aotta/SD-1000/Source/CVBasic/logo.bas

	' TMSColor 2.2.1 Mar/29/2024
	' Command: C:\Users\Andrea\Documents\Retrocomputer\SEGA\SG-1000\CVBasic\tmscolor.exe -z -b -p1 sega_logo6.bmp logo.bas 
	' Created: Sun Apr 14 18:44:49 2024

image_bitmap:
	DATA BYTE $7a,$00,$ba,$eb,$02,$00,$03,$0f
	DATA BYTE $1f,$3f,$7f,$06,$0a,$7f,$ff,$ff
	DATA BYTE $80,$02,$07,$ba,$03,$00,$07,$02
	DATA BYTE $f8,$f8,$fb,$3f,$3f,$3e,$07,$46
	DATA BYTE $1f,$0c,$e0,$80,$e6,$17,$28,$04
	DATA BYTE $07,$00,$07,$07,$1f,$0f,$7f,$fc
	DATA BYTE $e0,$c0,$45,$17,$01,$00,$21,$07
	DATA BYTE $c0,$00,$c1,$c3,$c3,$90,$37,$50
	DATA BYTE $f0,$c0,$80,$80,$07,$e0,$f8,$fc
	DATA BYTE $fe,$0f,$07,$f2,$6b,$0f,$d5,$7e
	DATA BYTE $00,$c0,$ab,$61,$03,$00,$f0,$e0
	DATA BYTE $01,$ac,$83,$86,$0c,$00,$ff,$7f
	DATA BYTE $c0,$fd,$04,$1f,$ec,$1e,$0c,$00
	DATA BYTE $3e,$fc,$38,$00,$86,$83,$12,$03
	DATA BYTE $30,$60,$40,$40,$41,$41,$e6,$17
	DATA BYTE $07,$00,$fc,$06,$06,$fe,$03,$fe
	DATA BYTE $80,$03,$07,$0c,$18,$36,$00,$15
	DATA BYTE $1a,$7f,$7f,$01,$04,$fd,$04,$c7
	DATA BYTE $90,$00,$cf,$00,$df,$df,$87,$38
	DATA BYTE $0f,$0c,$1f,$30,$83,$85,$8a,$61
	DATA BYTE $06,$00,$30,$30,$80,$80,$0a,$97
	DATA BYTE $e0,$00,$d5,$d4,$f4,$27,$03,$14
	DATA BYTE $ab,$00,$86,$80,$a0,$c1,$e0,$36
	DATA BYTE $f0,$7f,$fc,$26,$0f,$08,$81,$07
	DATA BYTE $01,$80,$87,$0f,$18,$0c,$f8,$06
	DATA BYTE $00,$78,$78,$38,$40,$33,$00,$7f
	DATA BYTE $03,$50,$97,$71,$00,$fe,$8f,$03
	DATA BYTE $18,$15,$00,$60,$00,$3c,$98,$04
	DATA BYTE $fc,$06,$e1,$e1,$03,$e9,$fc,$12
	DATA BYTE $36,$f0,$00,$e1,$f1,$0a,$13,$f0
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
	DATA BYTE $c1,$fb,$c0,$07,$63,$61,$71,$30
	DATA BYTE $38,$40,$18,$07,$81,$c9,$f9,$f3
	DATA BYTE $03,$68,$06,$fc,$1c,$83,$39,$77
	DATA BYTE $5f,$f8,$06,$07,$67,$77,$7e,$3c
	DATA BYTE $8e,$df,$38,$af,$b9,$a0,$07,$87
	DATA BYTE $36,$81,$81,$f6,$9e,$fb,$0f,$5d
	DATA BYTE $d6,$00,$ff,$ff,$ff,$ff,$c0

image_color:
	DATA BYTE $1a,$f1,$ba,$eb,$3b,$00,$e1,$00
	DATA BYTE $41,$06,$e5,$51,$51,$a3,$07,$51
	DATA BYTE $c5,$07,$e5,$00,$e6,$07,$fc,$17
	DATA BYTE $e5,$dd,$3b,$17,$4f,$d2,$0f,$07
	DATA BYTE $fb,$6b,$57,$db,$f5,$b6,$a2,$00
	DATA BYTE $75,$51,$03,$04,$73,$03,$cc,$51
	DATA BYTE $da,$17,$07,$dc,$17,$fb,$19,$ee
	DATA BYTE $17,$fd,$ee,$24,$32,$be,$04,$00
	DATA BYTE $fc,$25,$d6,$19,$d5,$de,$fe,$ef
	DATA BYTE $07,$ae,$9d,$c3,$c1,$cd,$05,$f3
	DATA BYTE $00,$4e,$fd,$e9,$f7,$cd,$00,$75
	DATA BYTE $ef,$ff,$34,$00,$9d,$ba,$02,$dd
	DATA BYTE $0c,$f5,$3a,$ff,$1e,$20,$fb,$1f
	DATA BYTE $7b,$27,$7c,$37,$bf,$15,$34,$fd
	DATA BYTE $09,$fb,$7d,$55,$f1,$ff,$f1,$e3
	DATA BYTE $9d,$f1,$b7,$dc,$bb,$0f,$04,$ad
	DATA BYTE $a4,$15,$f3,$1f,$f3,$37,$fe,$1f
	DATA BYTE $fb,$0f,$ed,$77,$7f,$7f,$1a,$00
	DATA BYTE $a1,$aa,$9b,$80,$9d,$00,$0c,$fd
	DATA BYTE $00,$f6,$24,$dd,$29,$2f,$be,$df
	DATA BYTE $00,$f7,$30,$db,$5f,$a6,$07,$7a
	DATA BYTE $08,$ad,$ff,$db,$6e,$ac,$a3,$a1
	DATA BYTE $f7,$f3,$00,$d5,$4f,$ff,$f3,$07
	DATA BYTE $7f,$bf,$2f,$bf,$3f,$fb,$37,$5d
	DATA BYTE $f5,$1b,$00,$a1,$7d,$00,$0a,$f6
	DATA BYTE $07,$e3,$17,$a1,$ef,$0f,$6f,$17
	DATA BYTE $ef,$07,$ad,$37,$22,$f3,$4f,$db
	DATA BYTE $57,$fe,$5f,$df,$b7,$07,$5c,$fe
	DATA BYTE $ef,$07,$6f,$66,$b7,$17,$76,$07
	DATA BYTE $ef,$5f,$7e,$67,$f5,$d7,$ef,$00
	DATA BYTE $ff,$ff,$ff,$fc
